XDjackieXD/TomoStrap/pebble/src/c/common.h

#pragma once

#define COLOR_BG_COLOR GColorBlack
#define COLOR_BG_BW GColorBlack

//#define COLOR_PULSE_BG_COLOR GColorIslamicGreen
#define COLOR_PULSE_BG_COLOR GColorRed
#define COLOR_PULSE_BG_BW GColorWhite

#define COLOR_PULSE_TEXT_COLOR GColorBlack
#define COLOR_PULSE_TEXT_BW GColorBlack

#define COLOR_OXIGEN_BG_COLOR GColorVividCerulean
#define COLOR_OXIGEN_BG_BW GColorWhite

#define COLOR_OXIGEN_TEXT_COLOR GColorBlack
#define COLOR_OXIGEN_TEXT_BW GColorBlack
